N0tTheMindProbe/Soil-Sensing-Device/examples/getValuesCO2/SensorDataTests11_20_2023_200ms.csv

time (ms) | CO2 (ppm) | 200ms delay
170641.00 | 509.22
170852.00 | 541.09
171063.00 | 536.88
171274.00 | 495.78
171485.00 | 533.59
171698.00 | 535.47
171909.00 | 492.5
172120.00 | 509.84
172331.00 | 524.06
172541.00 | 497.03
172752.00 | 499.69
172963.00 | 513.75
173174.00 | 506.25
173385.00 | 494.53
173598.00 | 502.81
173809.00 | 512.66
174020.00 | 497.03
174231.00 | 472.81
174442.00 | 517.03
174653.00 | 527.97
174864.00 | 503.28
175075.00 | 542.5
175286.00 | 540
175497.00 | 506.25
175710.00 | 535.78
175921.00 | 544.38
176132.00 | 504.22
176343.00 | 528.59
176553.00 | 546.25
176764.00 | 536.41
176975.00 | 525.47
177186.00 | 540.78
177397.00 | 540.78
177610.00 | 522.5
177821.00 | 518.59
178032.00 | 544.06
178243.00 | 526.88
178454.00 | 512.5
178665.00 | 541.41
178876.00 | 537.97
179087.00 | 502.81
179298.00 | 529.69
179509.00 | 542.19
179722.00 | 509.22
179933.00 | 521.88
180144.00 | 540.16
180355.00 | 529.84
180566.00 | 520.47
180776.00 | 535
180987.00 | 535.94
181198.00 | 515.47
181409.00 | 515.16
181622.00 | 536.72
181833.00 | 518.44
182044.00 | 499.53
182255.00 | 535.78
182466.00 | 530.47
182677.00 | 502.03
182888.00 | 529.69
183099.00 | 533.59
183310.00 | 498.59
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
